fitzterra/Cybot/doc/Images/20170601_064754.jpg

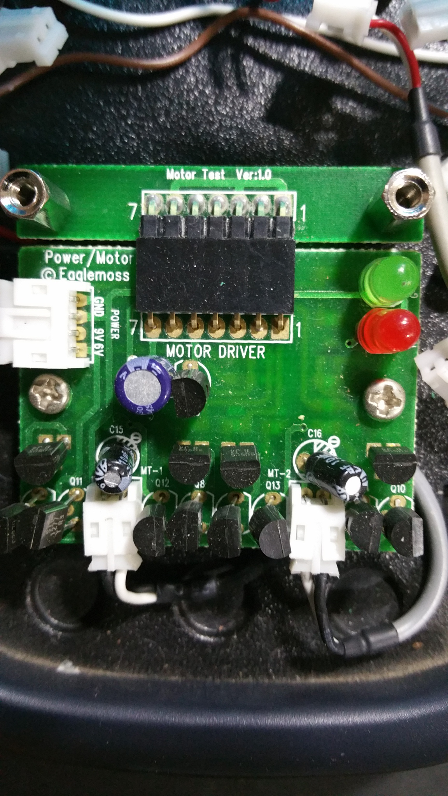
doc/Images/20170601_064754.jpg
