fitzterra/Cybot/doc/Images/MountArduino.jpg

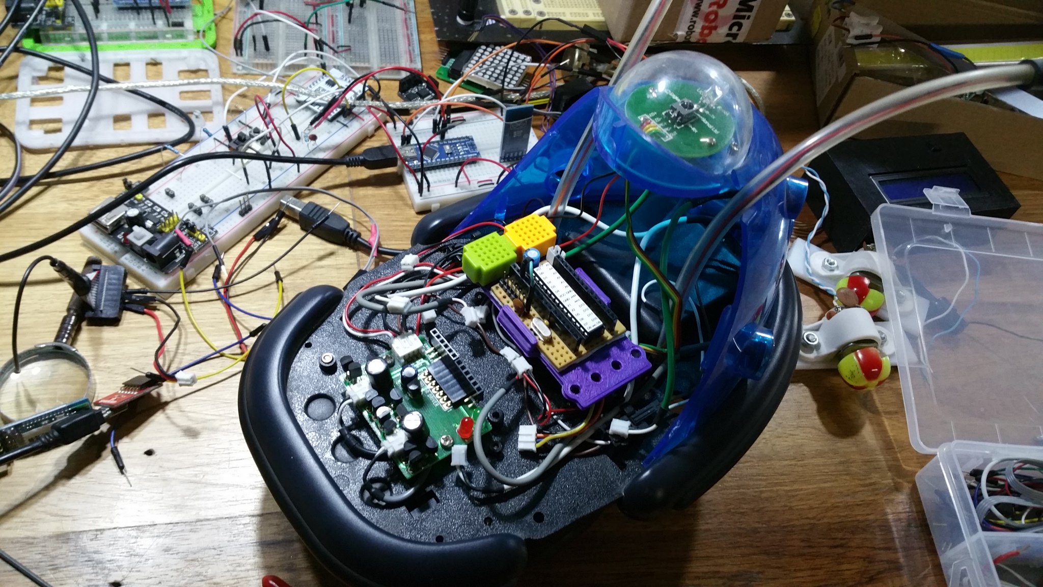
doc/Images/MountArduino.jpg
