fitzterra/Cybot/doc/Images/MountMCUBracket.jpg

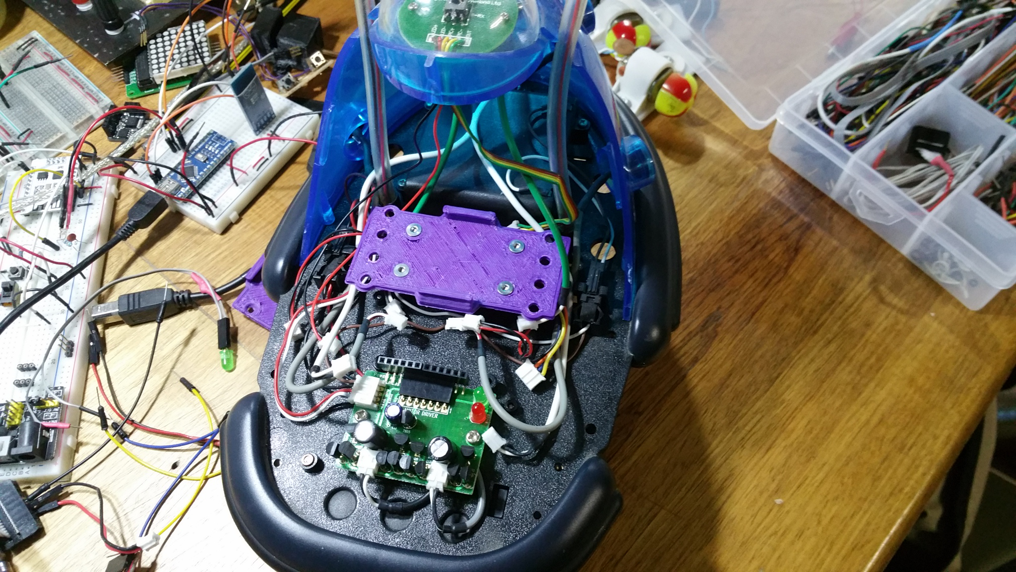
doc/Images/MountMCUBracket.jpg
