fitzterra/Cybot/firmware/debug.h

/*
 * Basic debug header.
 *
 * Define DEBUG before including this header to enable debugging.
 */

#include "config.h"
#include "Streaming.h"

// Macro to send debug details via the serial stream if DEBUG is defined.
#ifdef _DEBUG
	#define D(x) Serial << x
#else
	#define D(x)
#endif

#if (defined(SOFTSERIAL_EN) && defined(_DEBUG))
	#define DSS(x) SSerial << x
#else
	#define DSS(x)
#endif
